sn0oz/meteoboard/3d/led_ADA1376_dimensions.scad

// ADA1376 led strip dimensions
led_height = 0.2;
led_width = 10;
// 30 LEDs/m strip is 33.3 but can be adapted to reduce overall board footprint
led_interval = 33.3;
