sn0oz/meteoboard/3d/pcb_MB2_dimensions.scad

// mb2 PCB dimensions 
pcb_height = 3;
pcb_width = 40.7;
pcb_length = 143.3;
