sn0oz/meteoboard/3d/pir_SBC_dimensions.scad

// PIR SBC-PIR dimensions
pir_height = 1.65;
pir_width = 21;
pir_length = 40;
pir_lens_height = 8;
pir_lens_radius = 6;

pir_screw_hole_radius = 1.3;
pir_screw_hole_margin = 0.9;
