sn0oz/meteoboard/3d/psu_IRM-15-X_dimensions.scad

// 5V 3A IRM-15-5 dimensions 
psu_height = 24;
psu_width = 27.2;
psu_length = 52.4;
